jerryryle/odkey/src/nvs_odkey.c

#include "nvs_odkey.h"
#include "esp_log.h"
#include "nvs_flash.h"

static const char *TAG = "nvs_odkey";

bool nvs_odkey_init(void) {
    // Initialize NVS
    esp_err_t ret = nvs_flash_init();
    if (ret == ESP_ERR_NVS_NO_FREE_PAGES || ret == ESP_ERR_NVS_NEW_VERSION_FOUND) {
        ESP_LOGW(TAG, "NVS partition was truncated and needs to be erased");
        ret = nvs_flash_erase();
        if (ret != ESP_OK) {
            ESP_LOGE(TAG, "Failed to erase NVS: %s", esp_err_to_name(ret));
            return false;
        }
        ret = nvs_flash_init();
    }
    if (ret != ESP_OK) {
        ESP_LOGE(TAG, "Failed to initialize NVS: %s", esp_err_to_name(ret));
        return false;
    }

    // Create default namespace if it doesn't exist
    nvs_handle_t nvs_handle;
    ret = nvs_open(NVS_NAMESPACE, NVS_READWRITE, &nvs_handle);
    if (ret != ESP_OK) {
        ESP_LOGE(TAG,
                 "Failed to open NVS namespace '%s': %s",
                 NVS_NAMESPACE,
                 esp_err_to_name(ret));
        return false;
    }

    // Commit to ensure namespace is created
    ret = nvs_commit(nvs_handle);
    if (ret != ESP_OK) {
        ESP_LOGE(TAG, "Failed to commit NVS namespace: %s", esp_err_to_name(ret));
        nvs_close(nvs_handle);
        return false;
    }

    nvs_close(nvs_handle);
    ESP_LOGI(TAG, "NVS initialized and namespace '%s' created", NVS_NAMESPACE);
    return true;
}
